LulaUAV/Strelka-Flight-Computer/Simulations/Continuity_Test.asc

D1: diode; RRE02VTM6S
I1: current; 0.001; load
M1: pmos; AO6407
M2: pmos; AO6407
M3: nmos; AO6408
Q2: npn; 2N2222
R1: res; 1k
R2: res; 100k
R3: res; 1k
R4: res; 0.5
R7: res; 10k
R: res; 20
U2: UniversalOpamp2
V1: voltage; 3.3
V2: voltage; 3.3
V3: voltage; 4.2
V4: voltage; 0
V5: voltage; 3.3
V6: voltage; 0
Named nets: 0, Vr+, Vr-
.tran 0 5 0 0.01
.step param X list 0.0000001 1 3 5 7 9 10000
.lib "C:\\Users\\thean\\OneDrive\\Documents\\1. Uni Work\\HPR\\Strelka-Flight-Computer\\Simulations\\SPICE_Models\\lmx58_lm2904.lib"
R_Limit
.lib "C:\\Users\\Angus McLennan\\Documents\\1. Uni Work\\HPR\\Strelka-Flight-Computer\\Simulations\\SPICE_Models\\lmx58_lm2904.lib"
