LulaUAV/Strelka-Flight-Computer/Simulations/Ematch_Actuator.asc

M1: pmos; RSQ035P03
M2: nmos; AO6608_N
R1: res; 3
V1: voltage; 0
V2: voltage; 3.3
V3: voltage; 3.7
Named nets: 0
.tran 0 1 0 0.01
