LulaUAV/Strelka-Flight-Computer/SPI_Comms_Test/CM4/Core/Src/main.c

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
/* Includes ------------------------------------------------------------------*/
#include "main.h"
#include "string.h"

/* USER CODE BEGIN PD */

#ifndef HSEM_ID_0
#define HSEM_ID_0 (0U) /* HW semaphore 0*/
#endif
/* USER CODE END PD */

#if defined ( __ICCARM__ ) /*!< IAR Compiler */
#pragma location=0x30000000
ETH_DMADescTypeDef  DMARxDscrTab[ETH_RX_DESC_CNT]; /* Ethernet Rx DMA Descriptors */
#pragma location=0x30000200
ETH_DMADescTypeDef  DMATxDscrTab[ETH_TX_DESC_CNT]; /* Ethernet Tx DMA Descriptors */

#elif defined ( __CC_ARM )  /* MDK ARM Compiler */

__attribute__((at(0x30000000))) ETH_DMADescTypeDef  DMARxDscrTab[ETH_RX_DESC_CNT]; /* Ethernet Rx DMA Descriptors */
__attribute__((at(0x30000200))) ETH_DMADescTypeDef  DMATxDscrTab[ETH_TX_DESC_CNT]; /* Ethernet Tx DMA Descriptors */

#elif defined ( __GNUC__ ) /* GNU Compiler */
ETH_DMADescTypeDef DMARxDscrTab[ETH_RX_DESC_CNT] __attribute__((section(".RxDecripSection"))); /* Ethernet Rx DMA Descriptors */
ETH_DMADescTypeDef DMATxDscrTab[ETH_TX_DESC_CNT] __attribute__((section(".TxDecripSection")));   /* Ethernet Tx DMA Descriptors */

#endif

ETH_TxPacketConfig TxConfig;

CRC_HandleTypeDef hcrc;

ETH_HandleTypeDef heth;

SPI_HandleTypeDef hspi2;

UART_HandleTypeDef huart3;

/* USER CODE BEGIN PV */
#define BUFFER_SIZE 21
uint8_t RX_Buffer[BUFFER_SIZE];
uint8_t SPI_ready = 0;
/* USER CODE END PV */

static void MX_SPI2_Init(void);
/* USER CODE BEGIN 0 */
typedef struct {
	uint32_t servo_1_pos;
	uint32_t servo_2_pos;
	uint32_t servo_3_pos;
	uint32_t servo_4_pos;
}Servos_handle;

Servos_handle servos;
/* USER CODE END 0 */

/**
  * @brief  The application entry point.
  * @retval int
  */
int main(void)
{
/* USER CODE BEGIN Boot_Mode_Sequence_1 */
  /*HW semaphore Clock enable*/
  __HAL_RCC_HSEM_CLK_ENABLE();
  /* Activate HSEM notification for Cortex-M4*/
  HAL_HSEM_ActivateNotification(__HAL_HSEM_SEMID_TO_MASK(HSEM_ID_0));
  /*
  Domain D2 goes to STOP mode (Cortex-M4 in deep-sleep) waiting for Cortex-M7 to
  perform system initialization (system clock config, external memory configuration.. )
  */
  HAL_PWREx_ClearPendingEvent();
  HAL_PWREx_EnterSTOPMode(PWR_MAINREGULATOR_ON, PWR_STOPENTRY_WFE, PWR_D2_DOMAIN);
  /* Clear HSEM flag */
  __HAL_HSEM_CLEAR_FLAG(__HAL_HSEM_SEMID_TO_MASK(HSEM_ID_0));

/* USER CODE END Boot_Mode_Sequence_1 */
  /* MCU Configuration--------------------------------------------------------*/

  /* Reset of all peripherals, Initializes the Flash interface and the Systick. */
  HAL_Init();

  /* USER CODE BEGIN Init */
  MX_GPIO_Init();
  MX_USART3_UART_Init();
  MX_CRC_Init();
  /* USER CODE END Init */

  /* Initialize all configured peripherals */
  MX_SPI2_Init();
  /* USER CODE BEGIN 2 */
  HAL_SPI_Receive_IT(&hspi2, RX_Buffer, BUFFER_SIZE);

  HAL_UART_Transmit(&huart3, "Starting M4\r\n", sizeof("Starting M4\r\n"), HAL_MAX_DELAY);
  HAL_GPIO_WritePin(GPIOB, GPIO_PIN_14, GPIO_PIN_SET);
  HAL_Delay(500);
  HAL_GPIO_WritePin(GPIOB, GPIO_PIN_14, GPIO_PIN_RESET);

  hcrc.Instance = CRC;
  HAL_CRC_Init(&hcrc);
  /* USER CODE END 2 */

  /* Infinite loop */
  /* USER CODE BEGIN WHILE */
  while (1)
  {
    /* USER CODE END WHILE */

    /* USER CODE BEGIN 3 */
	  if(SPI_ready) {
		  SPI_ready = 0;
		  HAL_UART_Transmit(&huart3, "Received data\r\n", sizeof("Received data\r\n"), HAL_MAX_DELAY);
		  uint32_t CRC_Rec;
		  memcpy(&CRC_Rec, &RX_Buffer[sizeof(RX_Buffer)-4], sizeof(uint32_t));
		  uint32_t CRC_Calc = ~HAL_CRC_Calculate(&hcrc,(uint32_t *) RX_Buffer, sizeof(RX_Buffer)-4);
		  if(CRC_Calc == CRC_Rec){
			  uint8_t header = RX_Buffer[0];
			  if(header == 0x44) {
				  memcpy(&servos.servo_1_pos, &RX_Buffer[1], sizeof(servos.servo_1_pos));
				  memcpy(&servos.servo_2_pos, &RX_Buffer[5], sizeof(servos.servo_1_pos));
				  memcpy(&servos.servo_3_pos, &RX_Buffer[9], sizeof(servos.servo_1_pos));
				  memcpy(&servos.servo_4_pos, &RX_Buffer[13], sizeof(servos.servo_1_pos));

				  char printString[64];
				  size_t sz = snprintf(printString, sizeof(printString), "Servo Command Received: %d, %d, %d, %d\r\n", servos.servo_1_pos, servos.servo_2_pos, servos.servo_3_pos, servos.servo_4_pos);
				  HAL_UART_Transmit(&huart3, (uint8_t*)printString, sz, HAL_MAX_DELAY);
			  }
			  HAL_GPIO_WritePin(GPIOB, GPIO_PIN_14, GPIO_PIN_SET);
			  HAL_Delay(100);
		  }
	  }
	  HAL_GPIO_WritePin(GPIOB, GPIO_PIN_14, GPIO_PIN_RESET);
  }
  /* USER CODE END 3 */
}

/**
  * @brief CRC Initialization Function
  * @param None
  * @retval None
  */
void MX_CRC_Init(void)
{

  hcrc.Instance = CRC;
  hcrc.Init.DefaultPolynomialUse = DEFAULT_POLYNOMIAL_ENABLE;
  hcrc.Init.DefaultInitValueUse = DEFAULT_INIT_VALUE_ENABLE;
  hcrc.Init.InputDataInversionMode = CRC_INPUTDATA_INVERSION_NONE;
  hcrc.Init.OutputDataInversionMode = CRC_OUTPUTDATA_INVERSION_DISABLE;
  hcrc.InputDataFormat = CRC_INPUTDATA_FORMAT_BYTES;
  if (HAL_CRC_Init(&hcrc) != HAL_OK)
  {
    Error_Handler();
  }
}

/**
  * @brief ETH Initialization Function
  * @param None
  * @retval None
  */
void MX_ETH_Init(void)
{

   static uint8_t MACAddr[6];

  heth.Instance = ETH;
  MACAddr[0] = 0x00;
  MACAddr[1] = 0x80;
  MACAddr[2] = 0xE1;
  MACAddr[3] = 0x00;
  MACAddr[4] = 0x00;
  MACAddr[5] = 0x00;
  heth.Init.MACAddr = &MACAddr[0];
  heth.Init.MediaInterface = HAL_ETH_RMII_MODE;
  heth.Init.TxDesc = DMATxDscrTab;
  heth.Init.RxDesc = DMARxDscrTab;
  heth.Init.RxBuffLen = 1524;

  if (HAL_ETH_Init(&heth) != HAL_OK)
  {
    Error_Handler();
  }

  memset(&TxConfig, 0 , sizeof(ETH_TxPacketConfig));
  TxConfig.Attributes = ETH_TX_PACKETS_FEATURES_CSUM | ETH_TX_PACKETS_FEATURES_CRCPAD;
  TxConfig.ChecksumCtrl = ETH_CHECKSUM_IPHDR_PAYLOAD_INSERT_PHDR_CALC;
  TxConfig.CRCPadCtrl = ETH_CRC_PAD_INSERT;
}

/**
  * @brief SPI2 Initialization Function
  * @param None
  * @retval None
  */
static void MX_SPI2_Init(void)
{

  /* SPI2 parameter configuration*/
  hspi2.Instance = SPI2;
  hspi2.Init.Mode = SPI_MODE_SLAVE;
  hspi2.Init.Direction = SPI_DIRECTION_2LINES;
  hspi2.Init.DataSize = SPI_DATASIZE_8BIT;
  hspi2.Init.CLKPolarity = SPI_POLARITY_LOW;
  hspi2.Init.CLKPhase = SPI_PHASE_1EDGE;
  hspi2.Init.NSS = SPI_NSS_HARD_INPUT;
  hspi2.Init.FirstBit = SPI_FIRSTBIT_MSB;
  hspi2.Init.TIMode = SPI_TIMODE_DISABLE;
  hspi2.Init.CRCCalculation = SPI_CRCCALCULATION_DISABLE;
  hspi2.Init.CRCPolynomial = 0x0;
  hspi2.Init.NSSPMode = SPI_NSS_PULSE_DISABLE;
  hspi2.Init.NSSPolarity = SPI_NSS_POLARITY_LOW;
  hspi2.Init.FifoThreshold = SPI_FIFO_THRESHOLD_01DATA;
  hspi2.Init.TxCRCInitializationPattern = SPI_CRC_INITIALIZATION_ALL_ZERO_PATTERN;
  hspi2.Init.RxCRCInitializationPattern = SPI_CRC_INITIALIZATION_ALL_ZERO_PATTERN;
  hspi2.Init.MasterSSIdleness = SPI_MASTER_SS_IDLENESS_00CYCLE;
  hspi2.Init.MasterInterDataIdleness = SPI_MASTER_INTERDATA_IDLENESS_00CYCLE;
  hspi2.Init.MasterReceiverAutoSusp = SPI_MASTER_RX_AUTOSUSP_DISABLE;
  hspi2.Init.MasterKeepIOState = SPI_MASTER_KEEP_IO_STATE_DISABLE;
  hspi2.Init.IOSwap = SPI_IO_SWAP_DISABLE;
  if (HAL_SPI_Init(&hspi2) != HAL_OK)
  {
    Error_Handler();
  }
}

/**
  * @brief USART3 Initialization Function
  * @param None
  * @retval None
  */
void MX_USART3_UART_Init(void)
{

  huart3.Instance = USART3;
  huart3.Init.BaudRate = 115200;
  huart3.Init.WordLength = UART_WORDLENGTH_8B;
  huart3.Init.StopBits = UART_STOPBITS_1;
  huart3.Init.Parity = UART_PARITY_NONE;
  huart3.Init.Mode = UART_MODE_TX_RX;
  huart3.Init.HwFlowCtl = UART_HWCONTROL_NONE;
  huart3.Init.OverSampling = UART_OVERSAMPLING_16;
  huart3.Init.OneBitSampling = UART_ONE_BIT_SAMPLE_DISABLE;
  huart3.Init.ClockPrescaler = UART_PRESCALER_DIV1;
  huart3.AdvancedInit.AdvFeatureInit = UART_ADVFEATURE_NO_INIT;
  if (HAL_UART_Init(&huart3) != HAL_OK)
  {
    Error_Handler();
  }
  if (HAL_UARTEx_SetTxFifoThreshold(&huart3, UART_TXFIFO_THRESHOLD_1_8) != HAL_OK)
  {
    Error_Handler();
  }
  if (HAL_UARTEx_SetRxFifoThreshold(&huart3, UART_RXFIFO_THRESHOLD_1_8) != HAL_OK)
  {
    Error_Handler();
  }
  if (HAL_UARTEx_DisableFifoMode(&huart3) != HAL_OK)
  {
    Error_Handler();
  }
}

/**
  * @brief GPIO Initialization Function
  * @param None
  * @retval None
  */
void MX_GPIO_Init(void)
{
  GPIO_InitTypeDef GPIO_InitStruct = {0};

  /* GPIO Ports Clock Enable */
  __HAL_RCC_GPIOC_CLK_ENABLE();
  __HAL_RCC_GPIOB_CLK_ENABLE();
  __HAL_RCC_GPIOE_CLK_ENABLE();

  /*Configure GPIO pin Output Level */
  HAL_GPIO_WritePin(LD3_GPIO_Port, LD3_Pin, GPIO_PIN_RESET);

  /*Configure GPIO pin Output Level */
  HAL_GPIO_WritePin(LD2_GPIO_Port, LD2_Pin, GPIO_PIN_RESET);

  /*Configure GPIO pin : LD3_Pin */
  GPIO_InitStruct.Pin = LD3_Pin;
  GPIO_InitStruct.Mode = GPIO_MODE_OUTPUT_PP;
  GPIO_InitStruct.Pull = GPIO_PULLDOWN;
  GPIO_InitStruct.Speed = GPIO_SPEED_FREQ_LOW;
  HAL_GPIO_Init(LD3_GPIO_Port, &GPIO_InitStruct);

  /*Configure GPIO pin : LD2_Pin */
  GPIO_InitStruct.Pin = LD2_Pin;
  GPIO_InitStruct.Mode = GPIO_MODE_OUTPUT_PP;
  GPIO_InitStruct.Pull = GPIO_PULLDOWN;
  GPIO_InitStruct.Speed = GPIO_SPEED_FREQ_LOW;
  HAL_GPIO_Init(LD2_GPIO_Port, &GPIO_InitStruct);

}

/* USER CODE BEGIN 4 */
void HAL_SPI_RxCpltCallback(SPI_HandleTypeDef * hspi)
{
	SPI_ready = 1;
    HAL_SPI_Receive_IT(&hspi2, RX_Buffer, BUFFER_SIZE);
}
/* USER CODE END 4 */
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
